pablo-1424/TB_2023_Stoeri_FinalVersion/02_Code/EmbeddedSystem/TB_noLoRa/Core/Src/main.c

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
/* Includes ------------------------------------------------------------------*/
#include "main.h"

/* USER CODE BEGIN Includes */
#include <stdio.h>
#include <math.h>
#include "bma400func.h"
/* USER CODE END Includes */

I2C_HandleTypeDef hi2c1;

TIM_HandleTypeDef htim6;

UART_HandleTypeDef huart2;

/* USER CODE BEGIN PV */
uint16_t secondsOn;
uint8_t waterOn;
/* USER CODE END PV */

void SystemClock_Config(void);
static void MX_GPIO_Init(void);
static void MX_USART2_UART_Init(void);
static void MX_I2C1_Init(void);
static void MX_TIM6_Init(void);
/**
  * @brief  The application entry point.
  * @retval int
  */
int main(void)
{
  /* USER CODE BEGIN 1 */
	HAL_StatusTypeDef hStat;
	HAL_TIM_StateTypeDef tim6Status;

	uint8_t serialBuf[SER_BUF_SIZE] = {'\0'};
	uint8_t i2cBuf[8]={0};
	uint8_t i2cBufRet[FIFO_SIZE]={0};
	int16_t rawVal[3]={0};
	int16_t myVal[F_SAMP] = {0};
	int16_t fifoBytes = 0;
	int16_t nbrOverSize = 0;
	uint16_t timer_val = 0;

	secondsOn = 0;
	waterOn = 0;

	uint16_t currentMemPos = 0;


  /* USER CODE END 1 */

  /* MCU Configuration--------------------------------------------------------*/

  /* Reset of all peripherals, Initializes the Flash interface and the Systick. */
  HAL_Init();

  /* Configure the system clock */
  SystemClock_Config();

  /* Initialize all configured peripherals */
  MX_GPIO_Init();
  MX_USART2_UART_Init();
  MX_I2C1_Init();
  MX_TIM6_Init();
  /* USER CODE BEGIN 2 */

	sprintf(serialBuf, "Hello Boss   \r\n");
	HAL_UART_Transmit(&huart2, serialBuf, sizeof(serialBuf), HAL_MAX_DELAY);
	HAL_Delay(500);

    //Init sensor
    bma400_InitConfig();
    //HAL_TIM_Base_Start_IT(&htim6);
  /* USER CODE END 2 */

  /* Infinite loop */
  /* USER CODE BEGIN WHILE */
  while (1)
  {
  	  hStat = HAL_I2C_Mem_Read(&hi2c1, ACC_ADDR, REG_FIFO_LENGTH0, 1, i2cBufRet, 1, HAL_MAX_DELAY);
  	  if(hStat != HAL_OK){
  		  strcpy((char*)serialBuf, "Error Rx2    \r\n");
  		  HAL_UART_Transmit(&huart2, serialBuf, sizeof(serialBuf), HAL_MAX_DELAY);
  	  } else {
  		  fifoBytes = i2cBufRet[0];
  	  }
  	  hStat = HAL_I2C_Mem_Read(&hi2c1, ACC_ADDR, REG_FIFO_LENGTH1, 1, i2cBufRet, 1, HAL_MAX_DELAY);
  	  if(hStat != HAL_OK){
  		  strcpy((char*)serialBuf, "Error Rx     \r\n");
  		  HAL_UART_Transmit(&huart2, serialBuf, sizeof(serialBuf), HAL_MAX_DELAY);
  	  } else {
  		  fifoBytes = fifoBytes | i2cBufRet[0]<<8;
  	  }
	  hStat = HAL_I2C_Mem_Read(&hi2c1, ACC_ADDR, REG_FIFO_DATA, 1, i2cBufRet, fifoBytes, HAL_MAX_DELAY);
	  if(hStat != HAL_OK){
		  strcpy((char*)serialBuf, "Error Rx1    \r\n");
		  HAL_UART_Transmit(&huart2, serialBuf, sizeof(serialBuf), HAL_MAX_DELAY);
	  } else {
		  for(uint8_t i = 0; i<(fifoBytes/7); i++){
			  if(currentMemPos >= F_SAMP){
				  currentMemPos = 0;
				  nbrOverSize++;
			  }
			  for(uint8_t j = 0; j<3; j++){
				  rawVal[j] = i2cBufRet[1+i*7+j*2] | i2cBufRet[2+i*7+j*2]<<4;
				  if(i2cBufRet[2+i*7+j*2]>0x80){
					  rawVal[j] = rawVal[j] | 0xF<<12;
				  }
			  }
			  myVal[currentMemPos] = sqrt(pow(rawVal[0],2) + pow(rawVal[1],2) + pow(rawVal[2],2));
			  currentMemPos++;
		  }
		  uint8_t detection_count = 0;
		  tim6Status = HAL_TIM_Base_GetState(&htim6);
		  for(uint16_t i = 0; i < F_SAMP; i++){
			  if(myVal[i] < MIDDLE_VAL + THRESHOLD && myVal[i] > MIDDLE_VAL - THRESHOLD){
				  waterOn = 0;
				  HAL_TIM_Base_Stop_IT(&htim6);
				  timer_val = __HAL_TIM_GET_COUNTER(&htim6);
			  } else {
				  detection_count++;
				  if(detection_count >= MIN_COUNT){
					  waterOn = 1;
					  if(HAL_TIM_Base_GetState(&htim6) != HAL_TIM_STATE_BUSY){
						  HAL_TIM_Base_Start_IT(&htim6);
					  }
					  break;
				  }
			  }
		  }
	  }
	  if(waterOn == 0){
		  secondsOn = 0;
	  }

	  for(uint8_t i = 0; i<SER_BUF_SIZE; i++){
		  serialBuf[i] = 0;
	  }

	  if(currentMemPos == F_SAMP){
		  sprintf((char*)serialBuf, "%d,%d,%d%d\r\n", waterOn, myVal[F_SAMP - 1], secondsOn, currentMemPos+800*nbrOverSize);
	  } else {
		  sprintf((char*)serialBuf, "%d,%d,%d,%d\r\n", waterOn, myVal[currentMemPos], secondsOn, currentMemPos+800*nbrOverSize);
	  }
	  HAL_UART_Transmit(&huart2, serialBuf, sizeof(serialBuf), HAL_MAX_DELAY);

    /* USER CODE END WHILE */

    /* USER CODE BEGIN 3 */
  }
  /* USER CODE END 3 */
}

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
