pablo-1424/TB_2023_Stoeri_FinalVersion/02_Code/EmbeddedSystem/TB_Stoeri_FinalCode/stm32-it-sdk/Src/stm32l_sdk/timer/timer.c

/* ==========================================================
 * timer.c - Manage hardware timer functions
 * Project : Disk91 SDK
 * ----------------------------------------------------------
 * Created on: 26 nov. 2018
 *     Author: Paul Pinault aka Disk91
 * ----------------------------------------------------------
 * Copyright (C) 2018 Disk91
 *
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
 *
 *
 * ==========================================================
 */
#include <it_sdk/config.h>
#if ITSDK_PLATFORM == __PLATFORM_STM32L0
#if ITSDK_WITH_HW_TIMER != __TIMER_NONE
#include <it_sdk/debug.h>
#include <it_sdk/time/timer.h>
#include <stm32l_sdk/timer/timer.h>
#include "tim.h"
#include "main.h"


void __timer_enable_clk() {
	#if ITSDK_HW_TIMER1_ID == 21
		__HAL_RCC_TIM21_CLK_ENABLE();
	#elif ITSDK_HW_TIMER1_ID == 22
		__HAL_RCC_TIM22_CLK_ENABLE();
	#elif ITSDK_HW_TIMER1_ID == 1
		__HAL_RCC_TIM1_CLK_ENABLE();
	#elif  ITSDK_HW_TIMER1_ID == 2
		__HAL_RCC_TIM2_CLK_ENABLE();
	#elif  ITSDK_HW_TIMER1_ID == 3
		__HAL_RCC_TIM3_CLK_ENABLE();
	#elif  ITSDK_HW_TIMER1_ID == 4
		__HAL_RCC_TIM4_CLK_ENABLE();
	#elif  ITSDK_HW_TIMER1_ID == 6
		__HAL_RCC_TIM6_CLK_ENABLE();
	#elif  ITSDK_HW_TIMER1_ID == 7
		__HAL_RCC_TIM7_CLK_ENABLE();
	#endif
}

void __timer_disable_clk() {
	#if ITSDK_HW_TIMER1_ID == 21
		__HAL_RCC_TIM21_CLK_DISABLE();
	#elif ITSDK_HW_TIMER1_ID == 22
		__HAL_RCC_TIM22_CLK_DISABLE();
	#elif ITSDK_HW_TIMER1_ID == 1
		__HAL_RCC_TIM1_CLK_DISABLE();
	#elif  ITSDK_HW_TIMER1_ID == 2
		__HAL_RCC_TIM2_CLK_DISABLE();
	#elif  ITSDK_HW_TIMER1_ID == 3
		__HAL_RCC_TIM3_CLK_DISABLE();
	#elif  ITSDK_HW_TIMER1_ID == 4
		__HAL_RCC_TIM4_CLK_DISABLE();
	#elif  ITSDK_HW_TIMER1_ID == 6
		__HAL_RCC_TIM6_CLK_DISABLE();
	#elif  ITSDK_HW_TIMER1_ID == 7
		__HAL_RCC_TIM7_CLK_DISABLE();
	#endif
}
/*
int __timer_get_Irq() {
	#if ITSDK_HW_TIMER1_ID == 21
		return TIM21_IRQn;
	#elif ITSDK_HW_TIMER1_ID == 22
		return TIM21_IRQn;
	#elif ITSDK_HW_TIMER1_ID == 1
		return TIM1_IRQn;
	#elif  ITSDK_HW_TIMER1_ID == 2
		return TIM2_IRQn;
	#elif  ITSDK_HW_TIMER1_ID == 3
		return TIM3_IRQn;
	#elif  ITSDK_HW_TIMER1_ID == 4
		return TIM4_IRQn;
	#elif  ITSDK_HW_TIMER1_ID == 6
		return TIM6_IRQn;
	#elif  ITSDK_HW_TIMER1_ID == 7
		return TIM7_IRQn;
	#endif
}
*/

/**
 * Run the timer for the given time. Sync mode, return only after timer execution
 * At end the callback_func is called with value as parameter. If NULL the function
 * just return.
 */
itsdk_timer_return_t stm32l_hwtimer_sync_run(
		uint32_t ms,
		void (*callback_func)(uint32_t value),
		uint32_t value
) {
	__timer_enable_clk();

	// loop number
	uint32_t tics  = (ITSDK_HW_TIMER1_FREQ/1000) * ms;
	if ( tics == 0 ) return TIMER_TOO_SHORT;
	uint32_t loops = tics / ITSDK_HW_TIMER1_MAX;
	uint32_t initial = (tics - loops*ITSDK_HW_TIMER1_MAX);

	// first iteration
	ITSDK_HW_TIMER1_HANDLE.Init.Prescaler = 0;
	ITSDK_HW_TIMER1_HANDLE.Init.CounterMode = TIM_COUNTERMODE_UP;
	ITSDK_HW_TIMER1_HANDLE.Init.Period = initial;
	ITSDK_HW_TIMER1_HANDLE.Init.ClockDivision = TIM_CLOCKDIVISION_DIV1;
	HAL_TIM_Base_Init(&ITSDK_HW_TIMER1_HANDLE);
	__HAL_TIM_CLEAR_FLAG(&ITSDK_HW_TIMER1_HANDLE, TIM_FLAG_UPDATE);
	__HAL_TIM_ENABLE(&ITSDK_HW_TIMER1_HANDLE);
	while(__HAL_TIM_GET_FLAG(&ITSDK_HW_TIMER1_HANDLE,TIM_FLAG_UPDATE) == 0);
	__HAL_TIM_DISABLE(&ITSDK_HW_TIMER1_HANDLE);

	// loop for timer max duration
	ITSDK_HW_TIMER1_HANDLE.Init.Period = ITSDK_HW_TIMER1_MAX-1;
	HAL_TIM_Base_Init(&ITSDK_HW_TIMER1_HANDLE);
	__HAL_TIM_ENABLE(&ITSDK_HW_TIMER1_HANDLE);
	while ( loops > 0) {
		__HAL_TIM_CLEAR_FLAG(&ITSDK_HW_TIMER1_HANDLE, TIM_FLAG_UPDATE);
		while(__HAL_TIM_GET_FLAG(&ITSDK_HW_TIMER1_HANDLE,TIM_FLAG_UPDATE) == 0);
		loops--;
	}
	__HAL_TIM_DISABLE(&ITSDK_HW_TIMER1_HANDLE);

	__timer_disable_clk();
	if ( callback_func != NULL ) {
		callback_func(value);
	}

	return TIMER_INIT_SUCCESS;
}




volatile uint64_t __hwTimer_loop;
/**
 * Start a timer in background. the counter is set to 0 to be read
 * after to measure the durations. If the timer overrun, the duration
 * is added to a global counter.
 */
itsdk_timer_return_t stm32l_hwtimer_background_start() {
	ITSDK_HW_TIMER1_HANDLE.Init.Prescaler = 32000;
	ITSDK_HW_TIMER1_HANDLE.Init.CounterMode = TIM_COUNTERMODE_UP;
	ITSDK_HW_TIMER1_HANDLE.Init.Period = ITSDK_HW_TIMER1_MAX-1;
	ITSDK_HW_TIMER1_HANDLE.Init.ClockDivision = TIM_CLOCKDIVISION_DIV1;
	ITSDK_HW_TIMER1_HANDLE.Init.AutoReloadPreload = TIM_AUTORELOAD_PRELOAD_ENABLE;
	HAL_TIM_Base_Init(&ITSDK_HW_TIMER1_HANDLE);
	HAL_TIM_Base_Start_IT(&ITSDK_HW_TIMER1_HANDLE);
	__hwTimer_loop = 0;
	return TIMER_INIT_SUCCESS;

}

/**
 * get the duration of the period since the timer started in background.
 * the timer is stopped if the stop flag is set to BOOL_TRUE
 */
uint64_t stm32l_hwtimer_getDurationUs(itsdk_bool_e stop) {
	uint64_t tics_now = __HAL_TIM_GetCounter(&ITSDK_HW_TIMER1_HANDLE);
	if ( stop == BOOL_TRUE ) {
		HAL_TIM_Base_Stop_IT(&ITSDK_HW_TIMER1_HANDLE);
	}
	uint64_t tics_per_micro =  ( ITSDK_HW_TIMER1_FREQ / 1000000 );
	uint64_t tics_total = (__hwTimer_loop * ITSDK_HW_TIMER1_MAX) + tics_now;
	return tics_total / tics_per_micro;
}


/**
 * Timer interrupt handler to manage overflow duration
 */
void HAL_TIM_PeriodElapsedCallback(TIM_HandleTypeDef *htim) {
	if ( htim == &ITSDK_HW_TIMER1_HANDLE ) {
		__hwTimer_loop++;
	}
	// Condition added (P. Stoeri)
	if(htim == &htim6){
		timFunc(1);
	}
}


#endif
#endif
